UMRoboticsTeam/umrt-outreach-robotcar-wireless/ESP32_CameraServer_AP_2023_V1.3/camera_index.h

//File: index_ov3660.html.gz_CEP, Size: 21403
#define index_ov3660_html_gz_len_CEP 21403
const uint8_t index_ov3660_html_gz_CEP[] = {
    0x1F, 0x8B, 0x08, 0x00, 0x00, 0x00, 0x00, 0x00, 0x02, 0xFF, 0xED, 0x7D, 0xE9, 0x76, 0xDB, 0x46,
    0xB6, 0xEE, 0x7F, 0x3D, 0x45, 0x85, 0xE9, 0x13, 0x49, 0x1D, 0x12, 0xC2, 0x0C, 0x50, 0xB2, 0x94,
    0x2B, 0x4B, 0xF2, 0xD0, 0xB1, 0x63, 0xB7, 0x65, 0x67, 0xEA, 0x95, 0xE5, 0x40, 0x24, 0x44, 0xB1,
    0x4D, 0x12, 0x0C, 0x00, 0x6A, 0x70, 0x8E, 0x9F, 0xE3, 0x3E, 0xD0, 0x7D, 0xB1, 0xFB, 0xED, 0xAA,
    0xC2, 0x44, 0x82, 0x20, 0x48, 0x4A, 0xB4, 0x3B, 0xE7, 0x58, 0x89, 0x04, 0x14, 0xAA, 0x76, 0xED,
    0x79, 0x28, 0x14, 0x80, 0x47, 0x5F, 0x75, 0x83, 0x4E, 0x7C, 0x37, 0xF6, 0xD9, 0x55, 0x3C, 0x1C,
    0x1C, 0x6D, 0x3D, 0x12, 0x7F, 0x18, 0xFE, 0x3D, 0xBA, 0xF2, 0xBD, 0xAE, 0x38, 0xE4, 0xA7, 0x43,
    0x3F, 0xF6, 0x58, 0xE7, 0xCA, 0x0B, 0x23, 0x3F, 0x3E, 0x6C, 0x4C, 0xE2, 0xCB, 0x96, 0xDB, 0x98,
    0xBE, 0x3C, 0xF2, 0x86, 0xFE, 0x61, 0xE3, 0xBA, 0xEF, 0xDF, 0x8C, 0x83, 0x30, 0x6E, 0xB0, 0x4E,
    0x30, 0x8A, 0xFD, 0x11, 0xBA, 0xDF, 0xF4, 0xBB, 0xF1, 0xD5, 0x61, 0xD7, 0xBF, 0xEE, 0x77, 0xFC,
    0x16, 0x3F, 0x69, 0xF6, 0x47, 0xFD, 0xB8, 0xEF, 0x0D, 0x5A, 0x51, 0xC7, 0x1B, 0xF8, 0x87, 0x5A,
    0x1E, 0x56, 0xDC, 0x8F, 0x07, 0xFE, 0xD1, 0xBB, 0x97, 0x6F, 0xDE, 0xB2, 0x37, 0xC1, 0x45, 0x10,
    0x9F, 0x78, 0x21, 0x3B, 0x01, 0xA8, 0x30, 0x18, 0x0C, 0xFC, 0xF0, 0xD1, 0x9E, 0xB8, 0x9E, 0xF5,
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
    0xDC, 0x92, 0xFC, 0xBB, 0xF0, 0x2F, 0x83, 0xD0, 0x2F, 0xED, 0x99, 0xF4, 0x18, 0x04, 0x9D, 0x0F,
    0xAD, 0x28, 0xF6, 0xC2, 0xB8, 0x0E, 0x40, 0xEF, 0x32, 0x26, 0x0F, 0xB6, 0x08, 0x9E, 0x4F, 0x1A,
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
};
