UMRoboticsTeam/umrt-outreach-robotcar-wireless/ESP32_CameraServer_AP_2023_V1.3/config.h

// config.h
#ifndef CONFIG_H
#define CONFIG_H



// Wifi Channel: 1-13 generally
// 4 and 5 are confirmed fast - 10 is a little slow
#define WIFI_CHANNEL 5
// Wifi SSID 
#define WIFI_SSID "UMRT-CAR-1"
// Wifi pwd: "" for no password
#define WIFI_PWD "umrt2025"



#endif
