UMRoboticsTeam/umrt-outreach-robotcar-wireless/ESP32_CameraServer_AP_2023_V1.3/CameraWebServer_AP.h

/*
 * @Descripttion: 
 * @version: 
 * @Author: Elegoo
 * @Date: 2020-06-04 11:42:27
 * @LastEditors: Changhua
 * @LastEditTime: 2020-07-23 14:21:48
 */

#ifndef _CameraWebServer_AP_H
#define _CameraWebServer_AP_H
#include "esp_camera.h"
#include <WiFi.h>
#include "config.h"

class CameraWebServer_AP
{

public:
  void CameraWebServer_AP_Init(void);
  String wifi_name;

private:
  // const char *ssid = "ESP32_CAM";
  // const char *password = "elegoo2020";
  char *ssid = "UMRT-CAR-1";
  // char *ssid = UMRT;
  //char *password = "elegoo2020";
  char *password = "umrt2025";
  // char *password = WIFI_PWD;
};

#endif
